rasberryrabbit/MonitorLatencyChecker/SensorDesign/SensorDesign.kicad_sch

## KiCad design SensorDesign/SensorDesign.kicad_sch (2023-04-22, an earlier design)

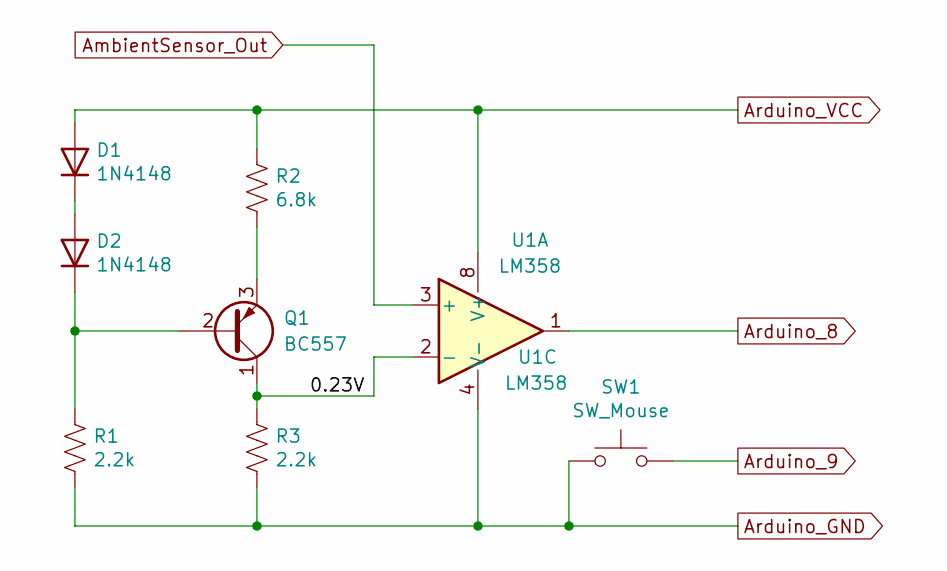
[picture p5: schematic SensorDesign.kicad_sch]

Parts:
D1, D2: 1N4148
Q1: BC557
R1, R3: 2.2k
R2: 6.8k
SW1: SW_Mouse
U1: LM358

Connections:
0.23V: Q1.1 (C), R3.1, U1.2 (-)
AmbientSensor_Out: U1.3 (+)
Arduino_8: U1.1
Arduino_9: SW1.2
Arduino_GND: R1.2, R3.2, SW1.1, U1.4 (V-)
Arduino_VCC: D1.2 (A), R2.1, U1.8 (V+)
unnamed: D1.1 (K), D2.2 (A)
unnamed: D2.1 (K), Q1.2 (B), R1.1
unnamed: Q1.3 (E), R2.2
